8076ducc/robocup-2025/open/mechanical design/rpi & camera/lens aligner.3mf

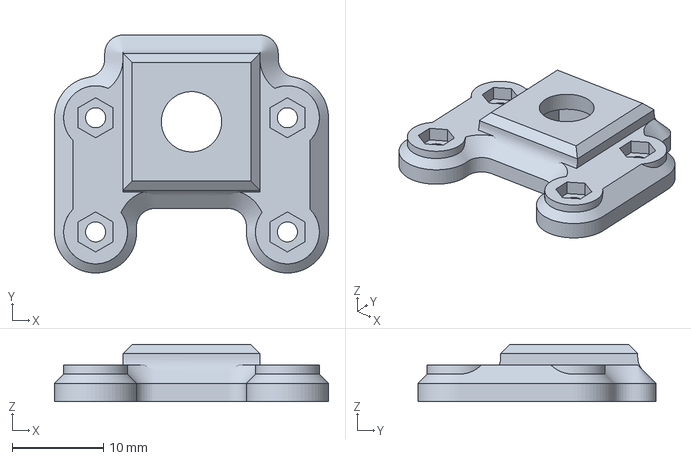
[picture p15: CAD file, 2025-03-22]
open/mechanical design/rpi & camera/lens aligner.3mf
30.0 x 26.1 x 6.25 mm
