8076ducc/robocup-2025/open/mechanical design/rpi & camera/nano b/rpi mount nano b.3mf

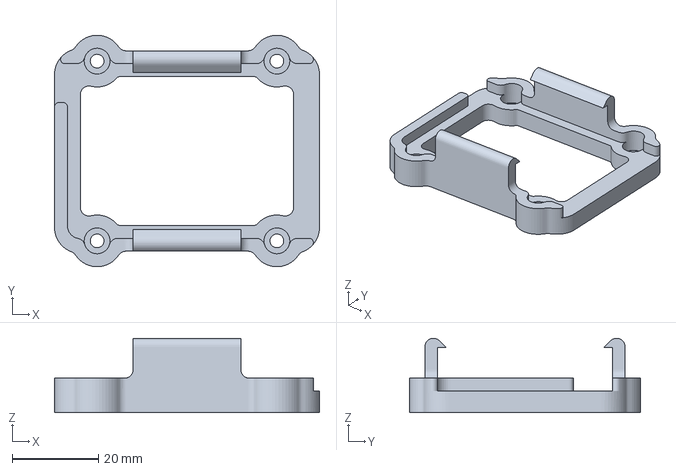
[picture p16: CAD file, 2025-02-21]
open/mechanical design/rpi & camera/nano b/rpi mount nano b.3mf
61.5 x 53.7 x 17.3 mm
