8076ducc/robocup-2025/open/mechanical design/spinning kicker/left plate.3mf

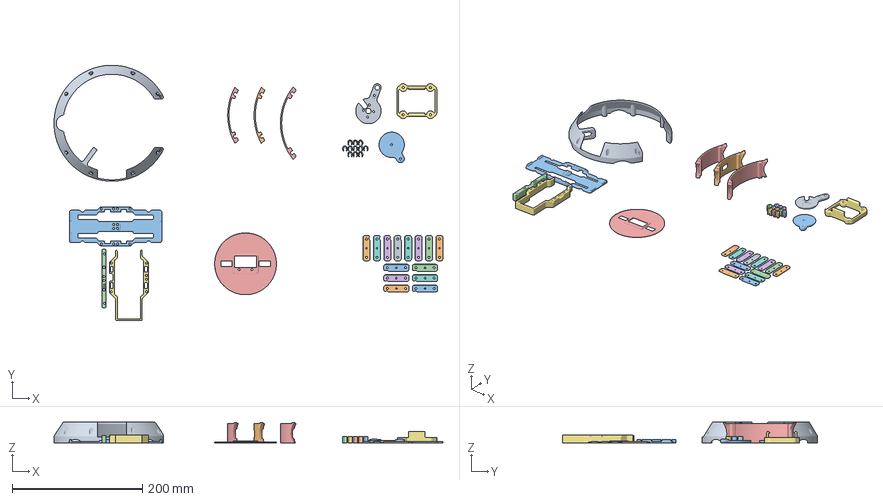
[picture p17: CAD file, 2025-02-01]
open/mechanical design/spinning kicker/left plate.3mf
597.6 x 392.4 x 32.0 mm
cover (layer 2)
motor spacer front x 4
driver cover (battery anti-short)
cover back (layer 1)
battery guide wall
motor spacer back left x 4
cover right (layer 1)
motor spacer back right x 6
layer 2 to 3 adapter
cover left (layer 1)
rpi mount
right plate
left plate
layer 1 short protection
wire clip x 11
