8076ducc/robocup-2025/open/mechanical design/wheel/4mm/wheel.3mf

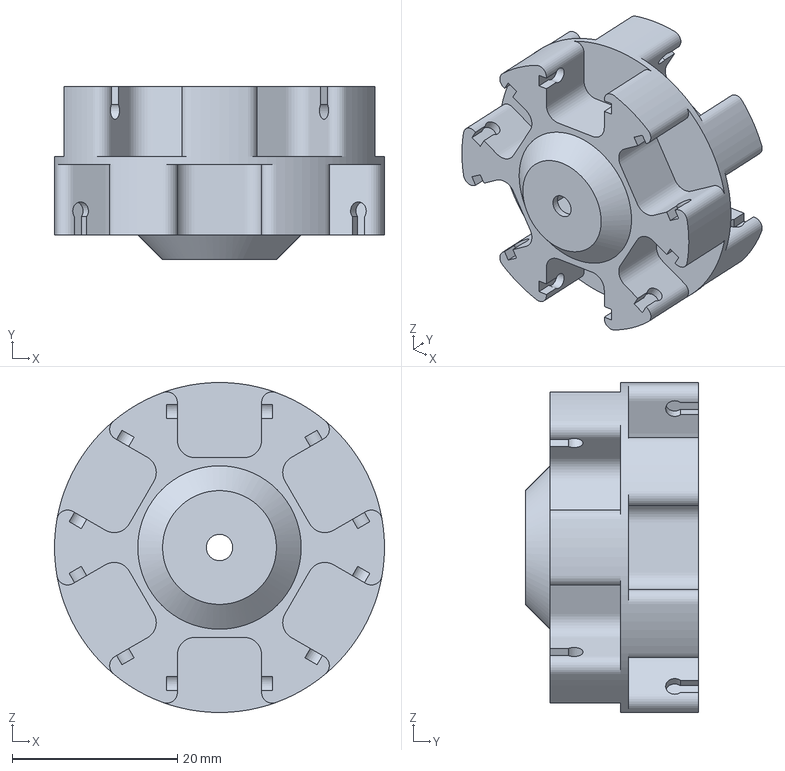
[picture p18: CAD file, 2025-06-07]
open/mechanical design/wheel/4mm/wheel.3mf
40.0 x 21.0 x 40.0 mm
