8076ducc/robocup-2025/open/mechanical design/wheel/5mm/wheel.3mf

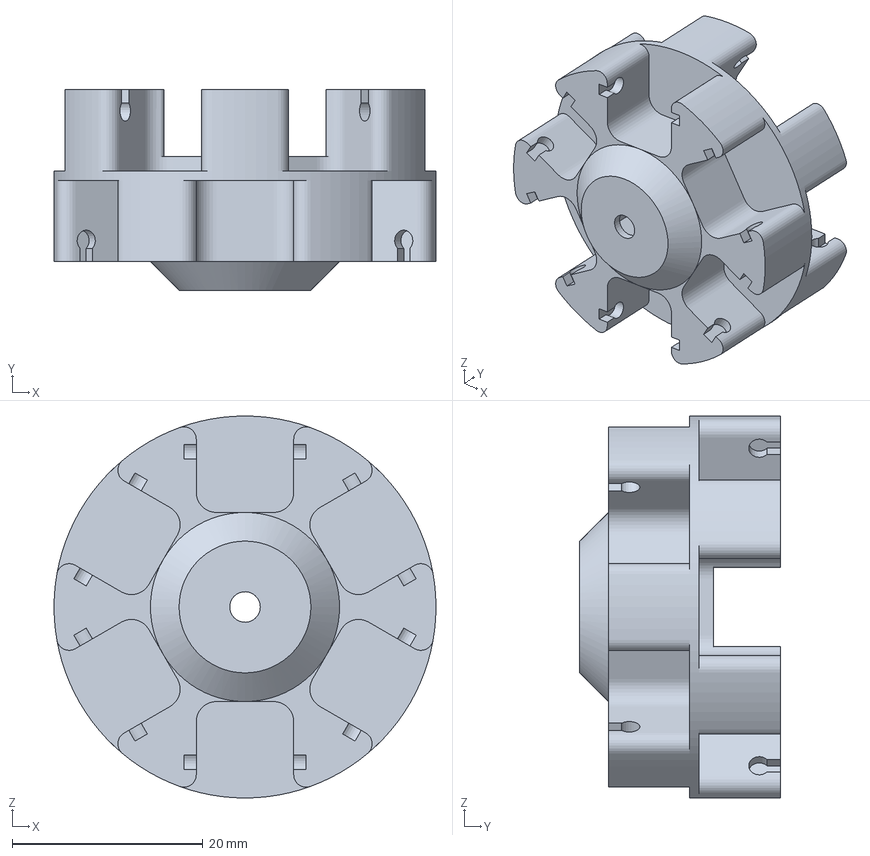
[picture p19: CAD file, 2025-02-01]
open/mechanical design/wheel/5mm/wheel.3mf
40.0 x 21.0 x 40.0 mm
