8076ducc/robocup-2025/open/mechanical design/wheel/motor spacer front.3mf

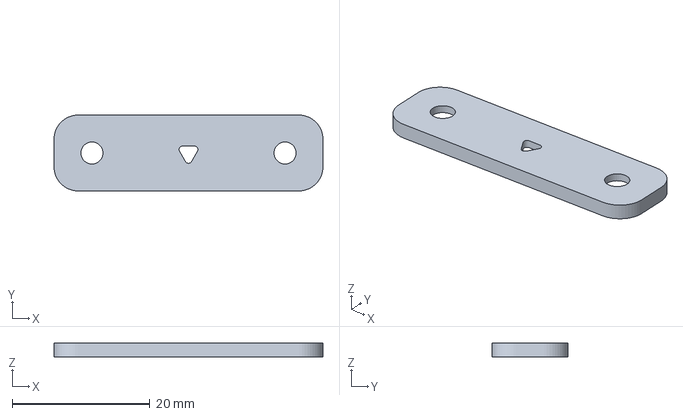
[picture p20: CAD file, 2025-02-01]
open/mechanical design/wheel/motor spacer front.3mf
39.0 x 11.0 x 2.00 mm
