8076ducc/robocup-2025/open/mechanical design/battery/battery guide wall.3mf

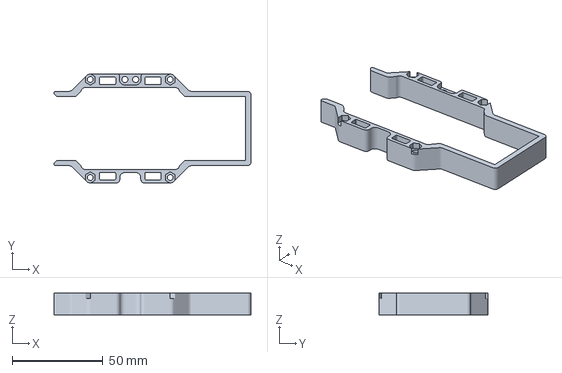
[picture p21: CAD file, 2025-01-22]
open/mechanical design/battery/battery guide wall.3mf
108.5 x 60.0 x 12.0 mm
