8076ducc/robocup-2025/open/mechanical design/cover/layer 1/servo mount.3mf

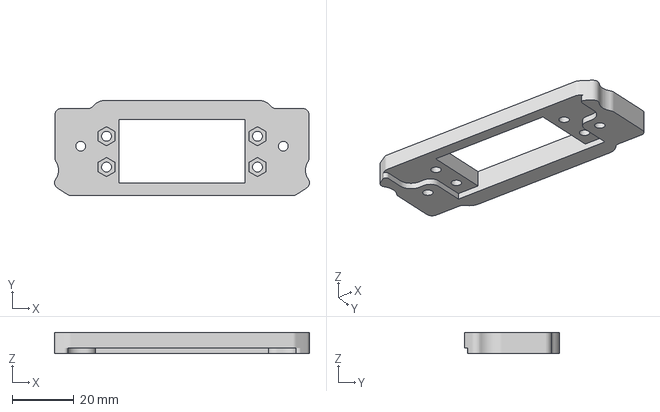
[picture p22: CAD file, 2025-03-22]
open/mechanical design/cover/layer 1/servo mount.3mf
82.8 x 30.9 x 6.90 mm
