8076ducc/robocup-2025/open/mechanical design/cover/layer 3/buck cover right.3mf

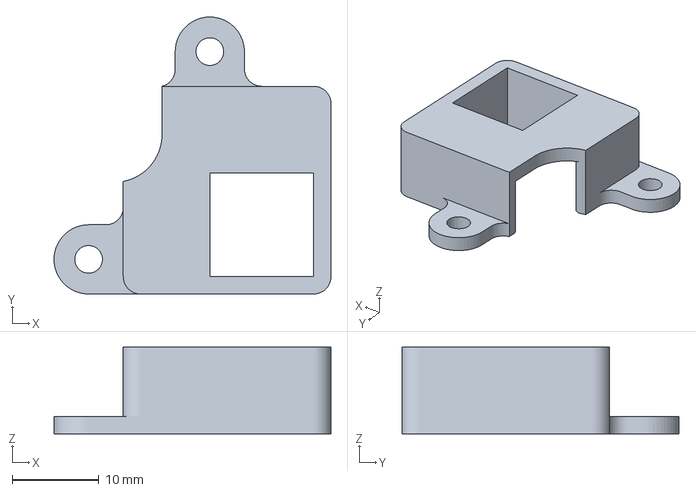
[picture p23: CAD file, 2025-06-07]
open/mechanical design/cover/layer 3/buck cover right.3mf
32.0 x 32.0 x 10.00 mm
