8076ducc/robocup-2025/open/mechanical design/kicker/ratchet.3mf

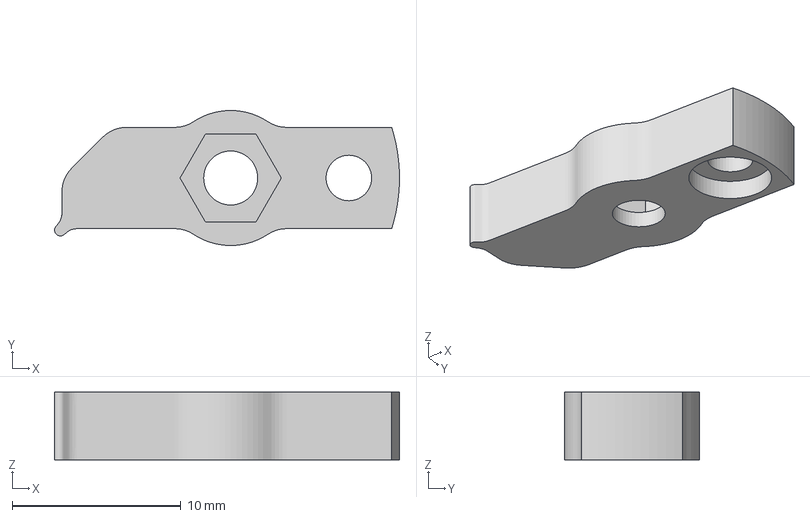
[picture p24: CAD file, 2025-06-07]
open/mechanical design/kicker/ratchet.3mf
20.4 x 8.00 x 4.00 mm
