8076ducc/robocup-2025/open/mechanical design/layer 4/layer 4.dxf

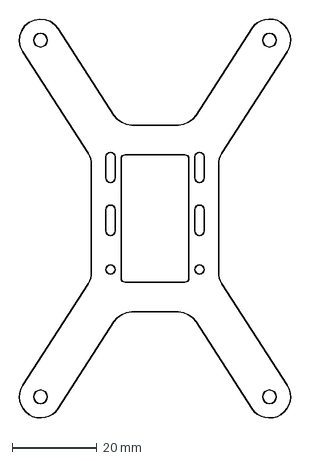
[picture p25: CAD file, 2025-03-12]
open/mechanical design/layer 4/layer 4.dxf
65.4 x 95.5 mm
