8076ducc/robocup-2025/open/mechanical design/layer 5/layer 5.1.dxf

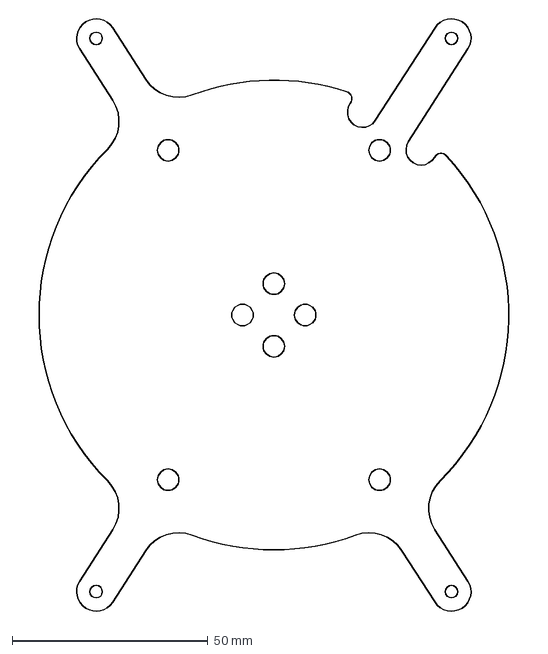
[picture p26: CAD file, 2025-03-12]
open/mechanical design/layer 5/layer 5.1.dxf
131.8 x 152.8 mm
