8076ducc/robocup-2025/open/mechanical design/rpi & camera/base a/rpi mount base a 7mm spacer.3mf

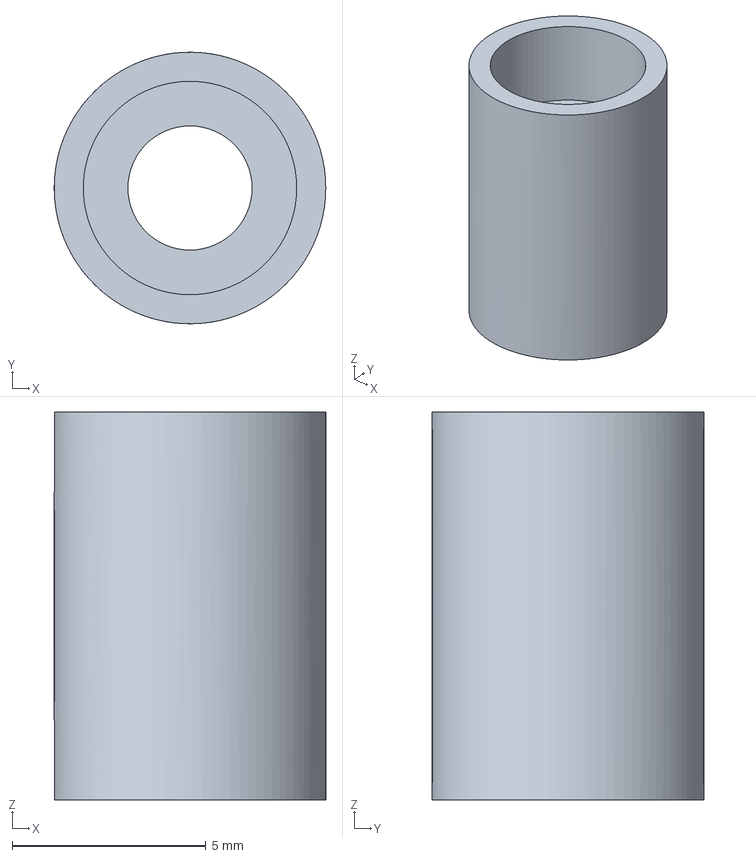
[picture p27: CAD file, 2025-03-03]
open/mechanical design/rpi & camera/base a/rpi mount base a 7mm spacer.3mf
7.00 x 7.00 x 10.0 mm
