8076ducc/robocup-2025/open/mechanical design/spinning kicker/right plate.3mf

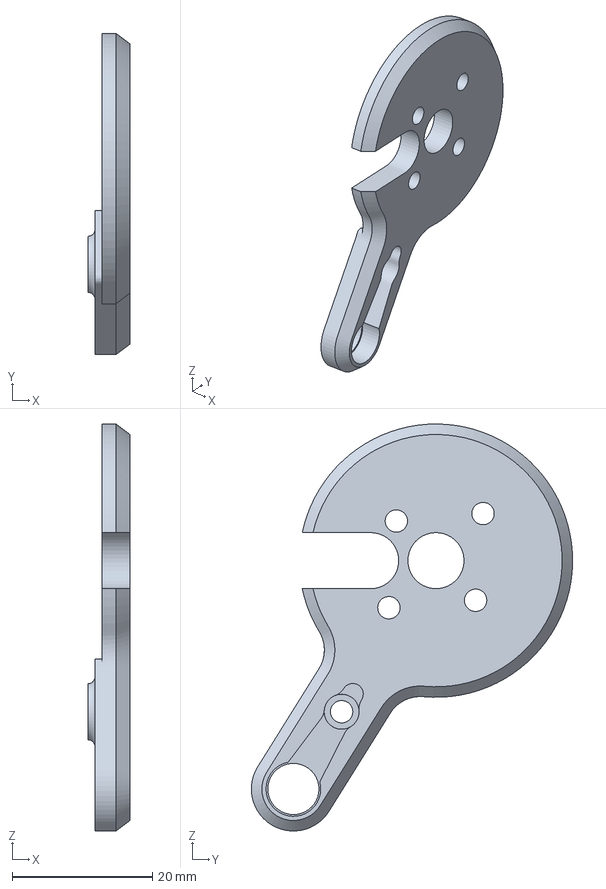
[picture p28: CAD file, 2025-02-01]
open/mechanical design/spinning kicker/right plate.3mf
6.00 x 45.8 x 58.1 mm
