8076ducc/robocup-2025/open/mechanical design/wheel/4mm/roller.3mf

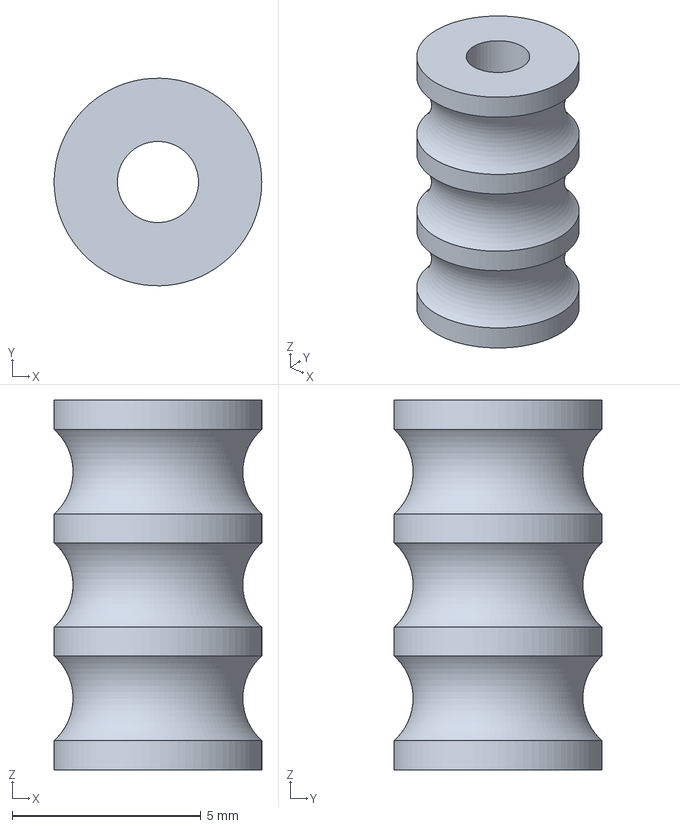
[picture p29: CAD file, 2025-03-03]
open/mechanical design/wheel/4mm/roller.3mf
5.50 x 5.50 x 9.80 mm
