8076ducc/robocup-2025/open/mechanical design/wheel/5mm/roller.3mf

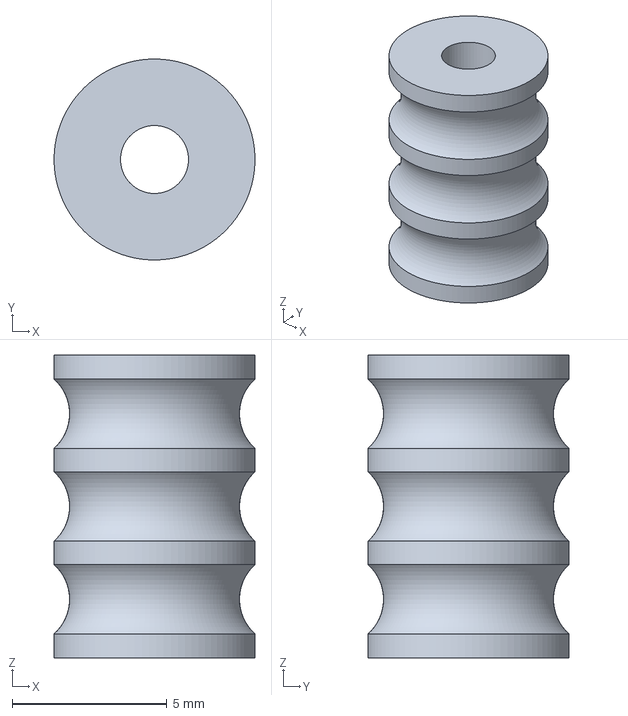
[picture p30: CAD file, 2025-01-22]
open/mechanical design/wheel/5mm/roller.3mf
6.50 x 6.50 x 9.80 mm
