8076ducc/robocup-2025/open/mechanical design/cover/layer 1/cover right (layer 1).3mf

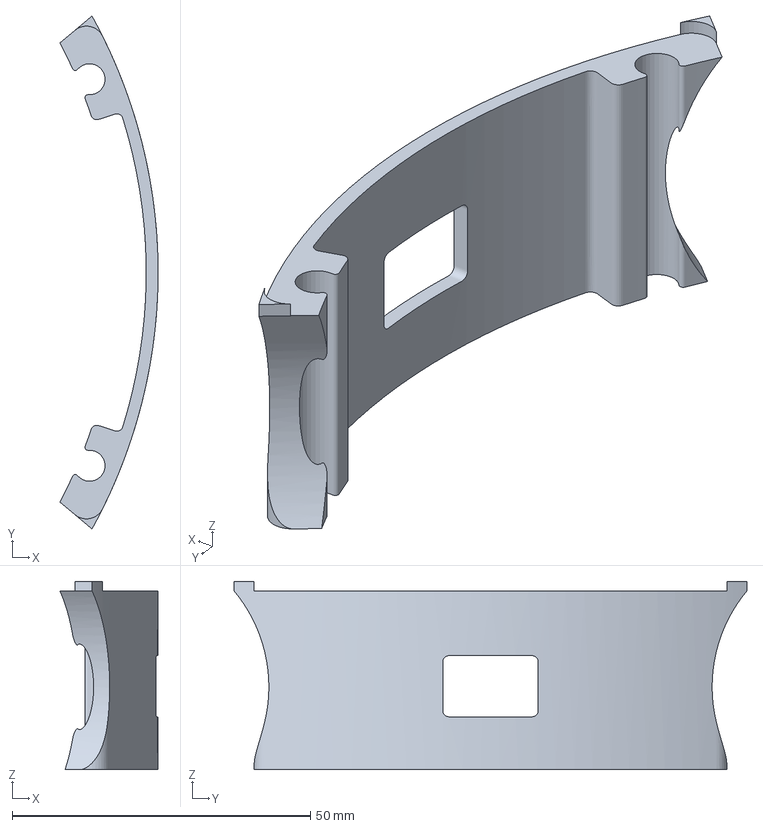
[picture p31: CAD file, 2025-02-01]
open/mechanical design/cover/layer 1/cover right (layer 1).3mf
16.5 x 86.1 x 31.6 mm
