8076ducc/robocup-2025/open/mechanical design/kicker/mirror sanding plate.3mf

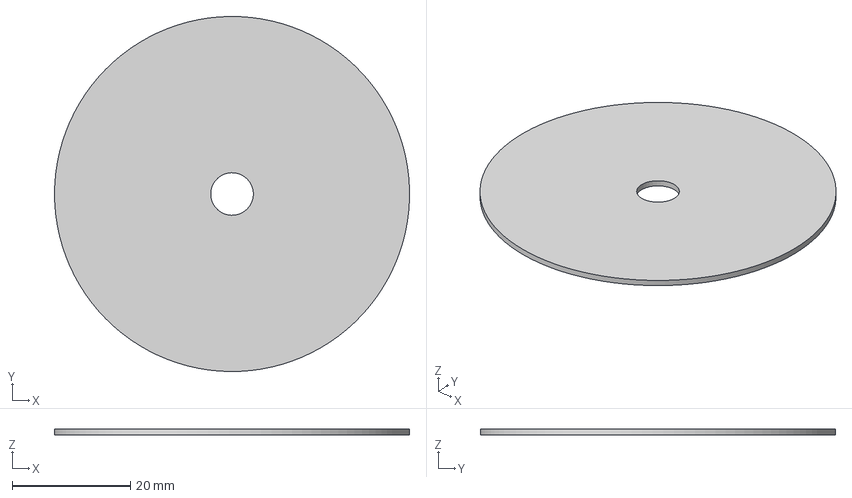
[picture p32: CAD file, 2025-06-07]
open/mechanical design/kicker/mirror sanding plate.3mf
60.0 x 60.0 x 1.00 mm
