8076ducc/robocup-2025/open/mechanical design/layer 5/layer 5.dxf

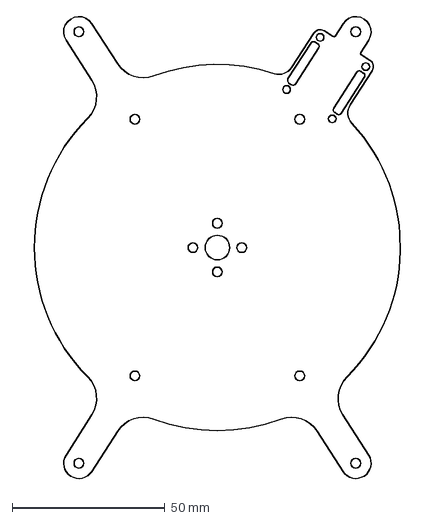
[picture p33: CAD file, 2025-03-12]
open/mechanical design/layer 5/layer 5.dxf
131.8 x 152.2 mm
