8076ducc/robocup-2025/open/mechanical design/misc/buck spacer.3mf

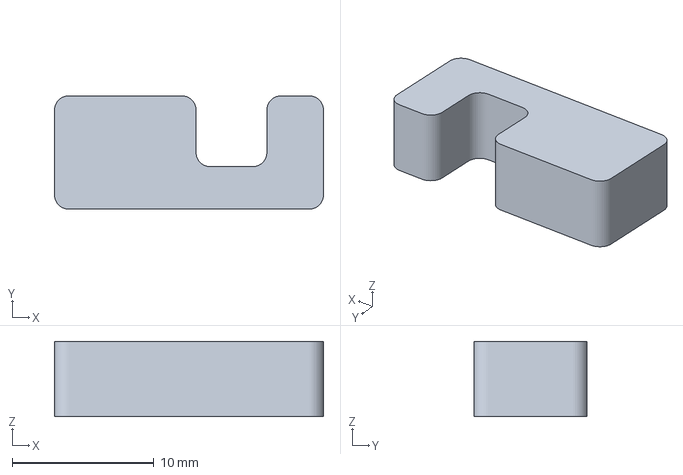
[picture p34: CAD file, 2025-06-07]
open/mechanical design/misc/buck spacer.3mf
19.0 x 8.00 x 5.30 mm
