8076ducc/robocup-2025/open/mechanical design/rpi & camera/base a/rpi mount base a lower.3mf

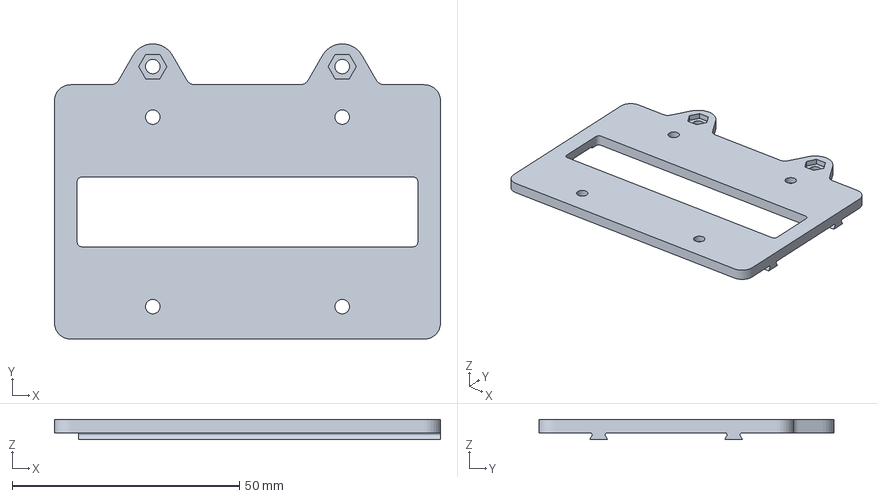
[picture p35: CAD file, 2025-02-28]
open/mechanical design/rpi & camera/base a/rpi mount base a lower.3mf
85.0 x 65.0 x 4.50 mm
