8076ducc/robocup-2025/open/mechanical design/spinning kicker/servo mount.3mf

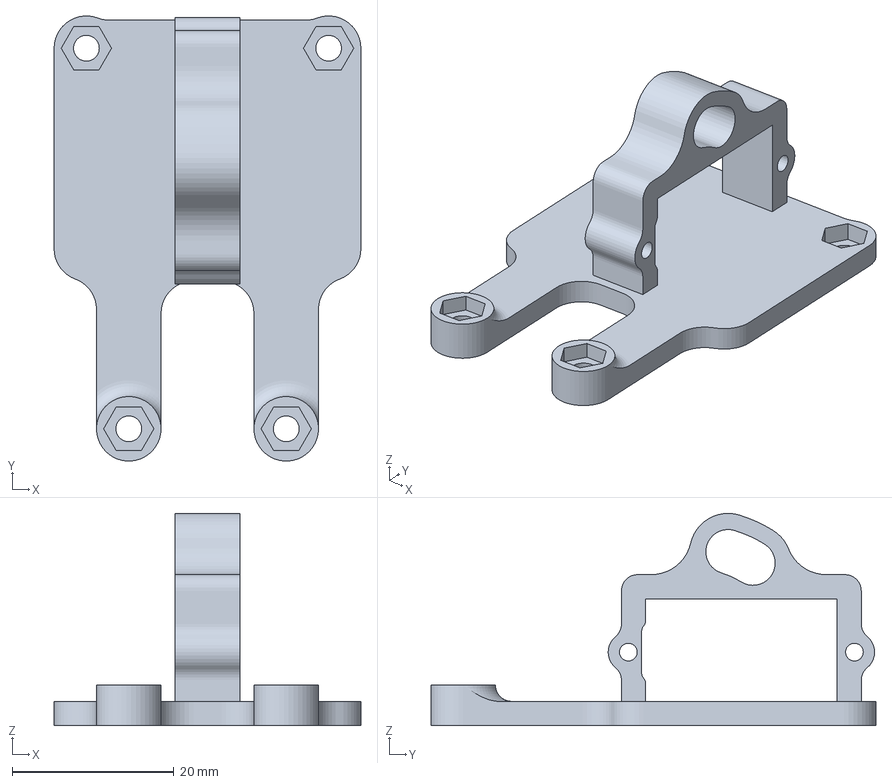
[picture p36: CAD file, 2025-02-01]
open/mechanical design/spinning kicker/servo mount.3mf
38.0 x 55.1 x 26.3 mm
