8076ducc/robocup-2025/open/mechanical design/cover/layer 1/cover left (layer 1).3mf

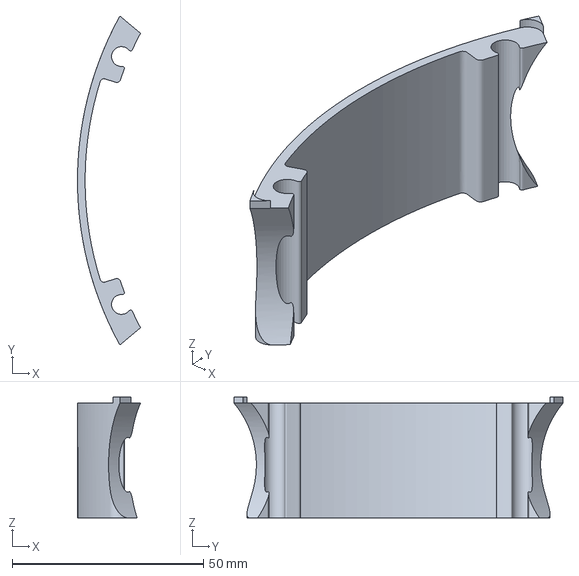
[picture p37: CAD file, 2025-01-11]
open/mechanical design/cover/layer 1/cover left (layer 1).3mf
16.5 x 86.1 x 31.6 mm
