8076ducc/robocup-2025/open/mechanical design/cover/layer 3/cover (layer 3).3mf

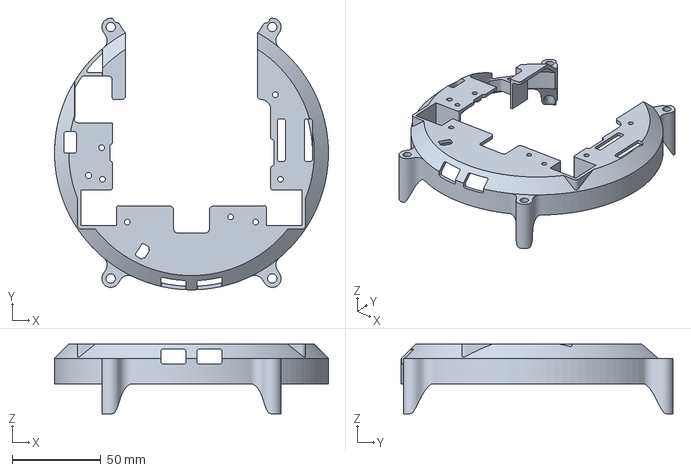
[picture p38: CAD file, 2025-06-07]
open/mechanical design/cover/layer 3/cover (layer 3).3mf
154.0 x 152.7 x 39.2 mm
