8076ducc/robocup-2025/open/mechanical design/kicker/gear rack.3mf

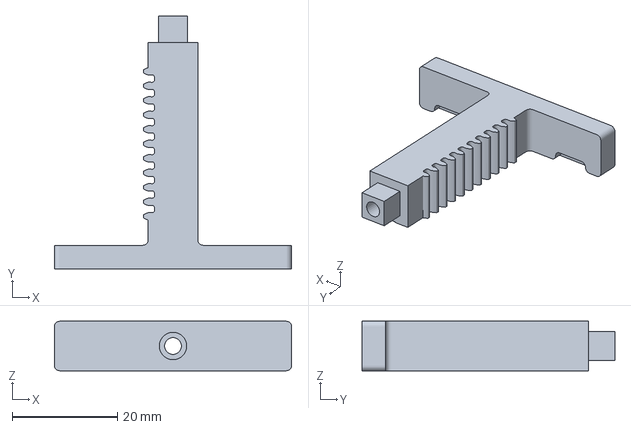
[picture p39: CAD file, 2025-06-07]
open/mechanical design/kicker/gear rack.3mf
45.0 x 48.0 x 9.40 mm
