8076ducc/robocup-2025/open/mechanical design/misc/mirror sawing plate.3mf

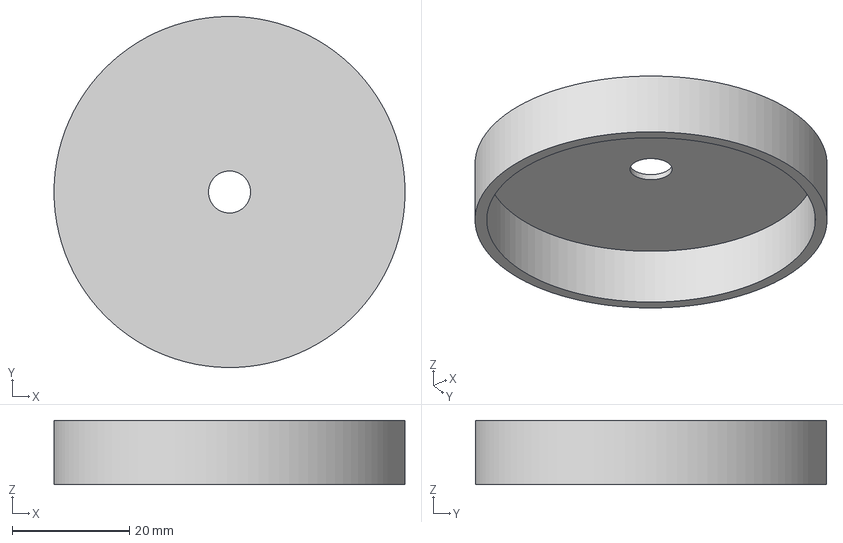
[picture p40: CAD file, 2025-06-07]
open/mechanical design/misc/mirror sawing plate.3mf
60.0 x 60.0 x 11.0 mm
