8076ducc/robocup-2025/open/mechanical design/rpi & camera/base a/ribbon cable clip.3mf

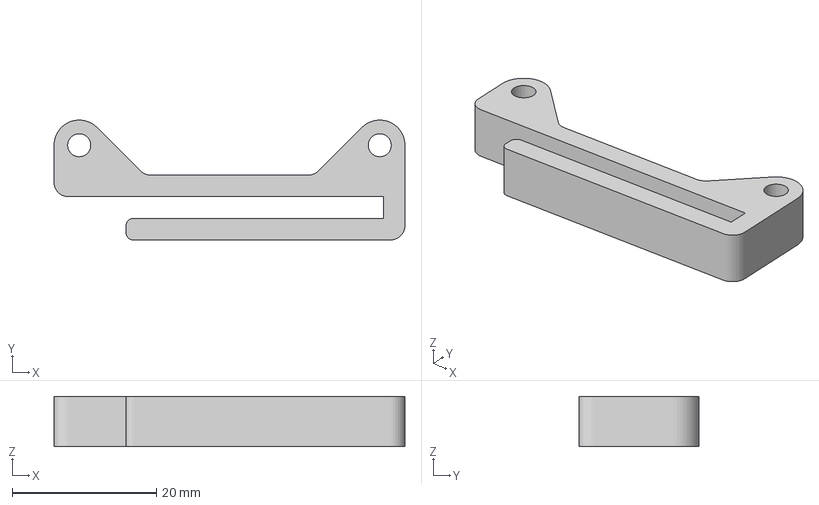
[picture p41: CAD file, 2025-02-21]
open/mechanical design/rpi & camera/base a/ribbon cable clip.3mf
48.7 x 16.6 x 7.00 mm
