8076ducc/robocup-2025/open/mechanical design/spinning kicker/mould lower.3mf

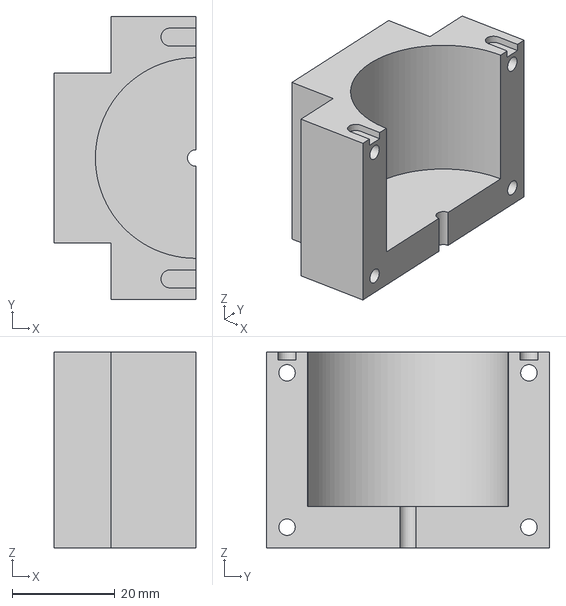
[picture p42: CAD file, 2025-01-22]
open/mechanical design/spinning kicker/mould lower.3mf
27.5 x 55.0 x 38.0 mm
