8076ducc/robocup-2025/open/mechanical design/cover/layer 1/cover back (layer 1).3mf

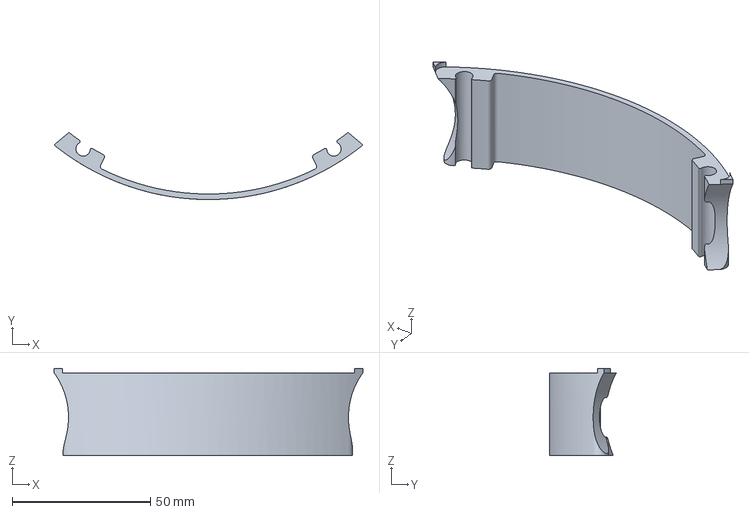
[picture p43: CAD file, 2025-01-11]
open/mechanical design/cover/layer 1/cover back (layer 1).3mf
111.8 x 24.3 x 31.6 mm
