8076ducc/robocup-2025/open/mechanical design/misc/layer 1 anti-short.3mf

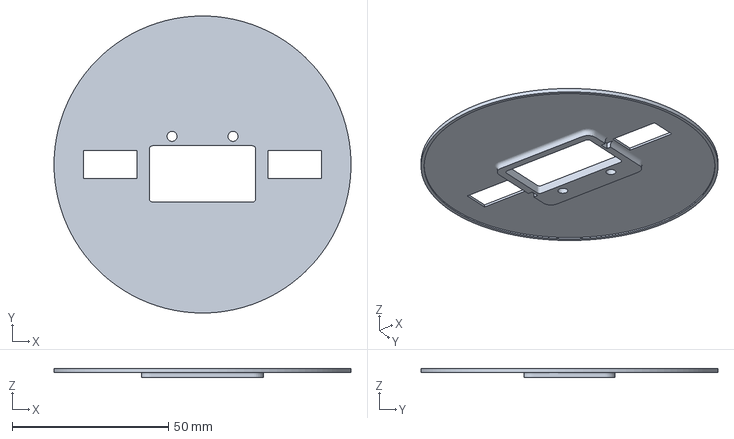
[picture p44: CAD file, 2025-02-21]
open/mechanical design/misc/layer 1 anti-short.3mf
95.0 x 95.0 x 2.80 mm
