8076ducc/robocup-2025/open/mechanical design/rpi & camera/base a/rpi mount base a 4mm spacer.3mf

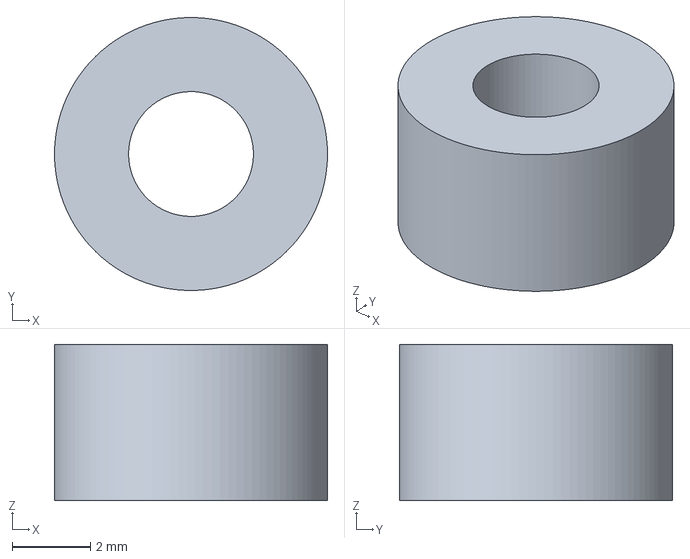
[picture p45: CAD file, 2025-02-21]
open/mechanical design/rpi & camera/base a/rpi mount base a 4mm spacer.3mf
7.00 x 7.00 x 4.00 mm
