8076ducc/robocup-2025/open/mechanical design/spinning kicker/mould cap.3mf

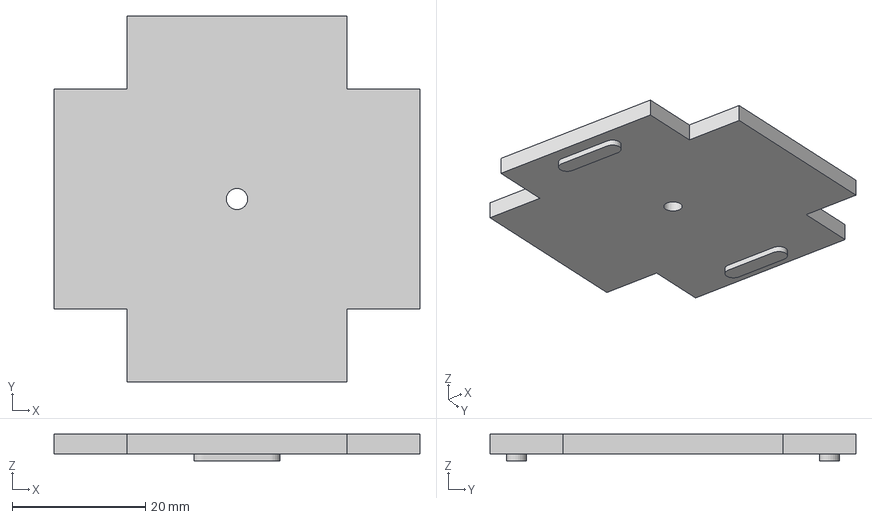
[picture p46: CAD file, 2025-01-22]
open/mechanical design/spinning kicker/mould cap.3mf
55.0 x 55.0 x 4.00 mm
