8076ducc/robocup-2025/open/mechanical design/kicker/bearing spacer.3mf

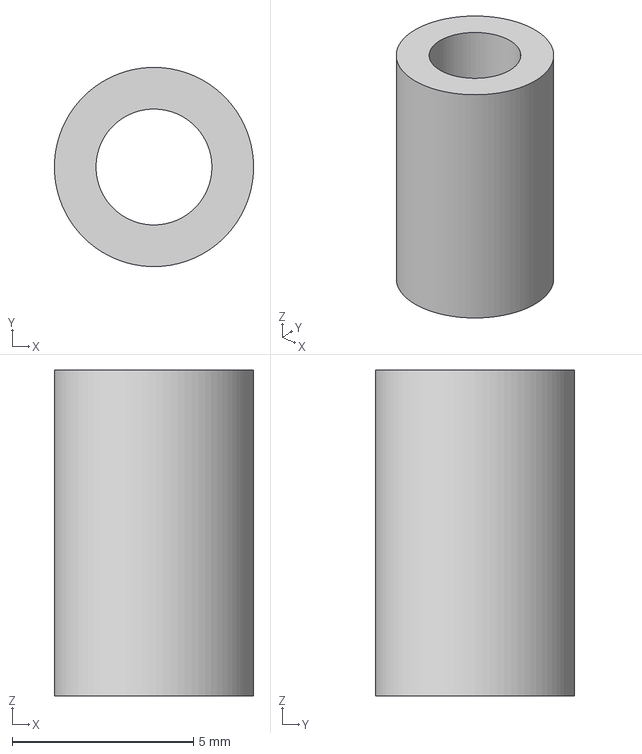
[picture p47: CAD file, 2025-06-07]
open/mechanical design/kicker/bearing spacer.3mf
5.50 x 5.50 x 9.00 mm
