8076ducc/robocup-2025/open/mechanical design/misc/buck support.3mf

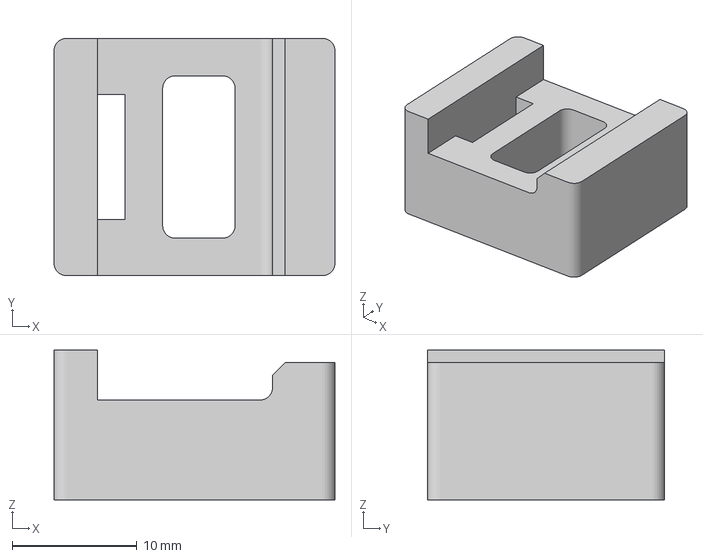
[picture p48: CAD file, 2025-02-21]
open/mechanical design/misc/buck support.3mf
22.5 x 19.0 x 12.0 mm
