8076ducc/robocup-2025/open/mechanical design/spinning kicker/roller.3mf

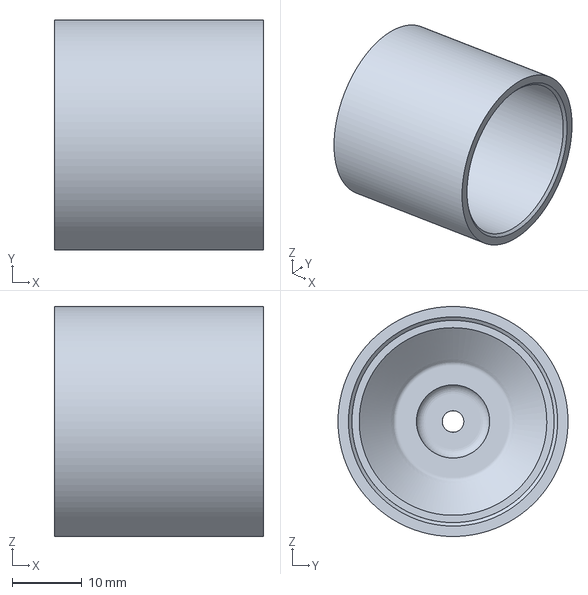
[picture p49: CAD file, 2025-01-22]
open/mechanical design/spinning kicker/roller.3mf
30.0 x 33.0 x 33.0 mm
