8076ducc/robocup-2025/open/mechanical design/kicker/ratchet (new).3mf

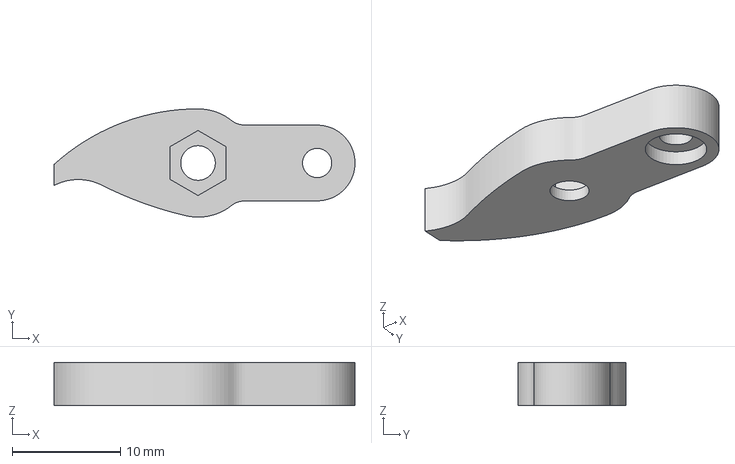
[picture p50: CAD file, 2025-06-07]
open/mechanical design/kicker/ratchet (new).3mf
27.8 x 10.00 x 4.00 mm
