8076ducc/robocup-2025/open/mechanical design/misc/layer 2 to 3 adapter.3mf

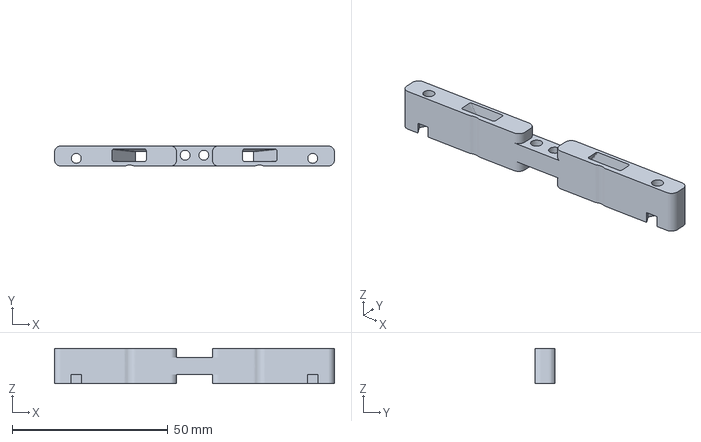
[picture p51: CAD file, 2025-02-01]
open/mechanical design/misc/layer 2 to 3 adapter.3mf
90.0 x 6.50 x 11.4 mm
