8076ducc/robocup-2025/open/mechanical design/kicker/slide case.3mf

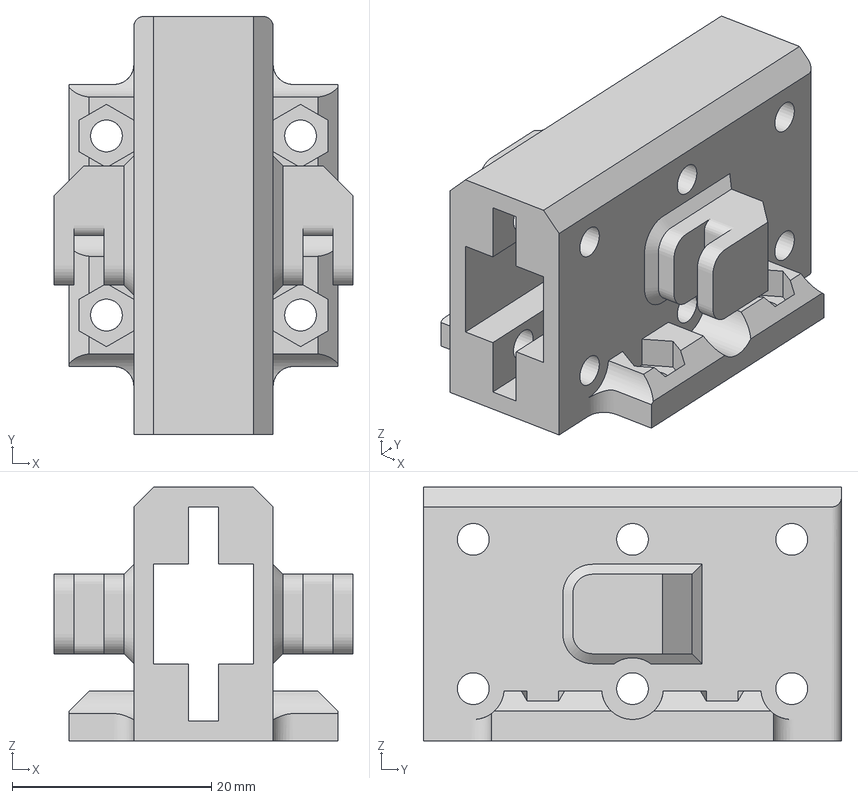
[picture p52: CAD file, 2025-06-07]
open/mechanical design/kicker/slide case.3mf
30.0 x 42.0 x 25.5 mm
