8076ducc/robocup-2025/open/mechanical design/misc/wire clip.3mf

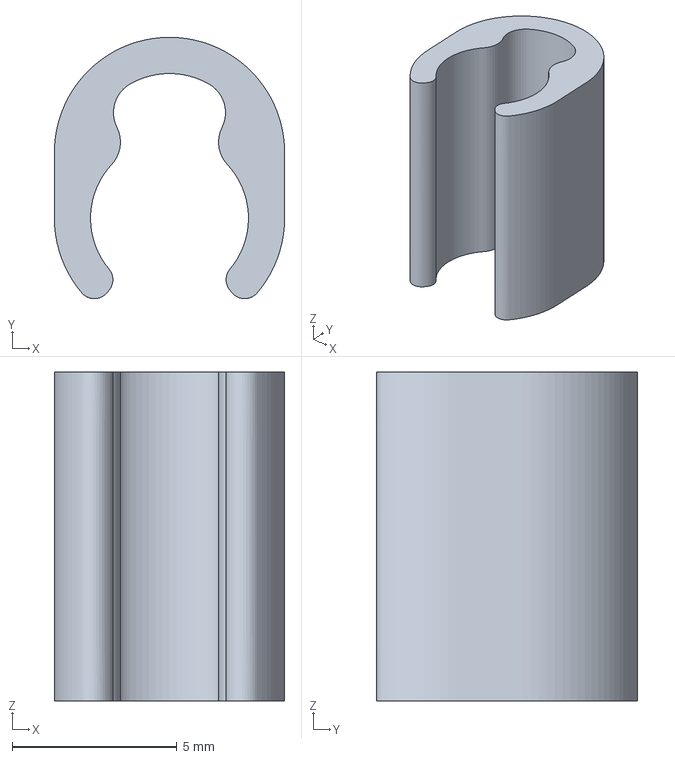
[picture p53: CAD file, 2025-01-22]
open/mechanical design/misc/wire clip.3mf
7.00 x 7.94 x 10.0 mm
