8076ducc/robocup-2025/open/mechanical design/kicker/slide.3mf

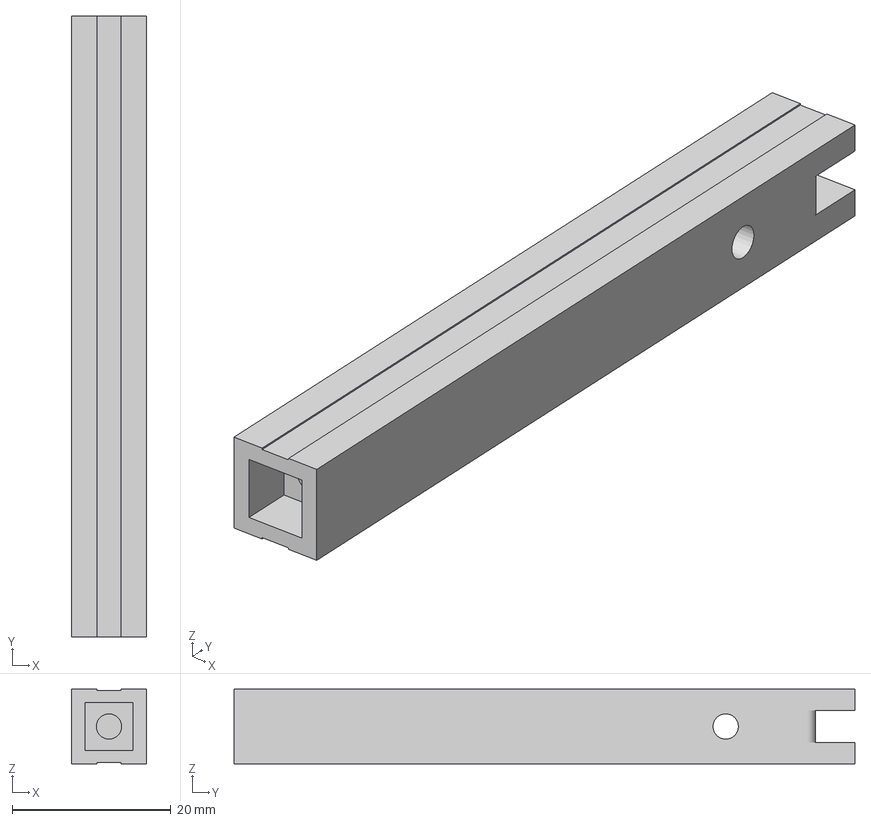
[picture p54: CAD file, 2025-06-07]
open/mechanical design/kicker/slide.3mf
9.40 x 78.3 x 9.40 mm
