8076ducc/robocup-2025/open/mechanical design/kicker/gear rack (extra teeth).3mf

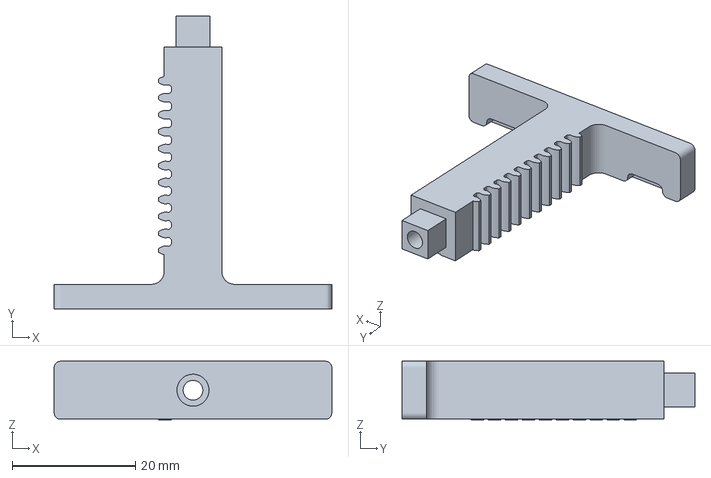
[picture p55: CAD file, 2025-06-07]
open/mechanical design/kicker/gear rack (extra teeth).3mf
45.0 x 47.5 x 9.50 mm
