8076ducc/robocup-2025/open/mechanical design/kicker/Spur Gear (12 teeth).3mf

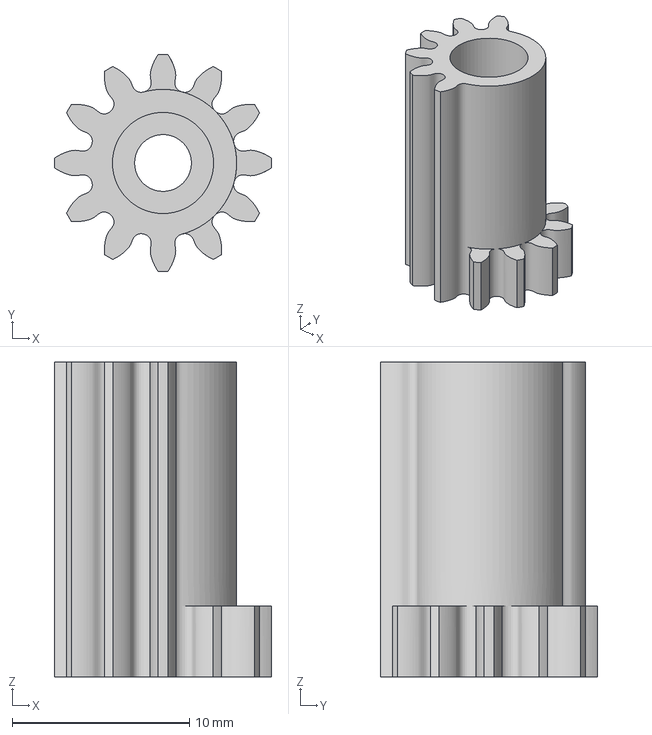
[picture p56: CAD file, 2025-06-07]
open/mechanical design/kicker/Spur Gear (12 teeth).3mf
12.2 x 12.2 x 17.8 mm
