8076ducc/robocup-2025/open/software design/microcontrollers/src/layer1/main.cpp

#include "main.h"
#include "light_ring.h"

PacketSerial TeensySerial;

Layer1TxDataUnion tx_data;
Layer1RxData rx_data;

LightRing light_ring;

void detectBall()
{
  Serial.println("Detect ball function running!");
  if (analogRead(LIGHTGATE) < ball_threshold)
  {
    tx_data.data.ball_in_catchment = true;
  }
  else
  {
    tx_data.data.ball_in_catchment = false;
  }
}

void onTeensyReceived(const byte *buf, size_t size)
{
  // Read the payload
  Layer1RxDataUnion data_received;
  // Don't continue if the payload is invalid
  if (size != sizeof(data_received))
  return;
  std::copy(buf, buf + size, std::begin(data_received.bytes));
  
  rx_data.line_track_ldr = data_received.data.line_track_ldr;
}

void setup()
{
  #ifdef SERIAL_DEBUG
  Serial.begin(serial_monitor_baud);
  while (!Serial)
  {
  }
  Serial.println("Debug serial connection established.");
  #endif
  
  light_ring.setup();
  pinMode(LIGHTGATE, INPUT);
  
  Serial0.begin(layer_1_serial_baud);
  // Serial0.setTxBufferSize(120);
  // Serial0.setRxBufferSize(120);
  while (!Serial0)
  {
  }
  TeensySerial.setStream(&Serial0);
  TeensySerial.setPacketHandler(&onTeensyReceived);
}

unsigned long last_time = 0;
int lowest = 3000;

void loop()
{
  #ifdef DEBUG
  //Serial.println("running Debug function::Calibrate");
  delay(150);
  // light_ring.calibrate();

  if (analogRead(LIGHTGATE) < lowest)
  {
    lowest = analogRead(LIGHTGATE);
  }
  Serial.println(analogRead(LIGHTGATE));
  Serial.print(lowest);
  Serial.print(" ");
  Serial.println(analogRead(LIGHTGATE));
  #else

  // Serial.println("im sending stuff to teensy1!");
  // TeensySerial.update();
  // Serial.println("attempting to run lightring_read");

  light_ring.read();
  detectBall();
  
  Serial.println("Sending data to Teensy1");
  TeensySerial.send(tx_data.bytes, sizeof(tx_data.bytes));
  #endif
}
