8076ducc/robocup-2025/open/software design/microcontrollers/src/layer1/main.h

#pragma once

#ifndef MAIN_H
#define MAIN_H

// #define DEBUG
// #define SERIAL_DEBUG
// #define BOT_A

#include <common.h>

#define S0 D2
#define S1 D3
#define S2 D4
#define S3 D5

#define MUX1 D0
#define MUX2 D1
#define LIGHTGATE D9

#define KICKER D10

// global variables

// TUNE THIS
const int ball_threshold = 1500;
// END TUNE

extern int line_track_ldr;
extern Layer1TxDataUnion tx_data;
extern Layer1RxData rx_data;

#endif
