8076ducc/robocup-2025/open/software design/microcontrollers/src/teensy1/camera.cpp

#include "main.h"

double field_width = 1580;
double field_height = 2190;

double regressGoal(double distance)
{
  return ((0 * pow(distance, 5)) + (0 * pow(distance, 4)) + (0.0017281976 * pow(distance, 3)) - (0.5748511944 * pow(distance, 2)) + (69.1097170904 * distance) - 2527.1180742143);
}

// store entire goal pose
void Robot::storeGoalPose(double yellow_goal_x, double yellow_goal_y, double blue_goal_x, double blue_goal_y)
{
  yellow_goal.current_pose.x = yellow_goal_x;
  yellow_goal.current_pose.y = yellow_goal_y;
  yellow_goal.current_pose.bearing = correctBearing(degrees(atan2(yellow_goal_x, yellow_goal_y)) + robot.current_pose.bearing);

  blue_goal.current_pose.x = blue_goal_x;
  blue_goal.current_pose.y = blue_goal_y;
  blue_goal.current_pose.bearing = correctBearing(degrees(atan2(blue_goal_x, blue_goal_y)) + robot.current_pose.bearing);
}

void Robot::storeYellowPose(double yellow_goal_x, double yellow_goal_y)
{
  yellow_goal.current_pose.x = yellow_goal_x;
  yellow_goal.current_pose.y = yellow_goal_y;
  yellow_goal.current_pose.bearing = correctBearing(degrees(atan2(yellow_goal_x, yellow_goal_y)) + robot.current_pose.bearing);
}

void Robot::storeBluePose(double blue_goal_x, double blue_goal_y)
{
  blue_goal.current_pose.x = blue_goal_x;
  blue_goal.current_pose.y = blue_goal_y;
  blue_goal.current_pose.bearing = correctBearing(degrees(atan2(blue_goal_x, blue_goal_y)) + robot.current_pose.bearing);
}

// store open goal pose
void Robot::storeGoalOpenPose(double yellow_open_x, double yellow_open_y, double blue_open_x, double blue_open_y)
{
  yellow_open.current_pose.x = yellow_open_x;
  yellow_open.current_pose.y = yellow_open_y;
  yellow_open.current_pose.bearing = correctBearing(degrees(atan2(yellow_open_x, yellow_open_y)) + robot.current_pose.bearing);

  blue_open.current_pose.x = blue_open_x;
  blue_open.current_pose.y = blue_open_y;
  blue_open.current_pose.bearing = correctBearing(degrees(atan2(blue_open_x, blue_open_y)) + robot.current_pose.bearing);
}

void Robot::storeYellowOpenPose(double yellow_open_x, double yellow_open_y)
{
  yellow_open.current_pose.x = yellow_open_x;
  yellow_open.current_pose.y = yellow_open_y;
  yellow_open.current_pose.bearing = correctBearing(degrees(atan2(yellow_open_x, yellow_open_y)) + robot.current_pose.bearing);
}

void Robot::storeBlueOpenPose(double blue_open_x, double blue_open_y)
{
  blue_open.current_pose.x = blue_open_x;
  blue_open.current_pose.y = blue_open_y;
  blue_open.current_pose.bearing = correctBearing(degrees(atan2(blue_open_x, blue_open_y)) + robot.current_pose.bearing);
}

void Robot::storeRobotPose()
{
  double ema_const = 0.2;

  double yellow_goal_real_dist = regressGoal(sqrt(pow(yellow_goal.current_pose.x, 2) + pow(yellow_goal.current_pose.y, 2)));
  double yellow_goal_real_x = yellow_goal_real_dist * sin(radians(yellow_goal.current_pose.bearing));
  double yellow_goal_real_y = yellow_goal_real_dist * cos(radians(yellow_goal.current_pose.bearing));

  double blue_goal_real_dist = regressGoal(sqrt(pow(blue_goal.current_pose.x, 2) + pow(blue_goal.current_pose.y, 2)));
  double blue_goal_real_x = blue_goal_real_dist * sin(radians(blue_goal.current_pose.bearing));
  double blue_goal_real_y = blue_goal_real_dist * cos(radians(blue_goal.current_pose.bearing));

  if (yellow_goal.detected && blue_goal.detected)
  {
    robot.current_pose.x = -(yellow_goal_real_x + blue_goal_real_x) / 2;
    robot.current_pose.y = -(yellow_goal_real_y + blue_goal_real_y) / 2;
  }
  else if (yellow_goal.detected)
  {
    robot.current_pose.x = -yellow_goal_real_x;

    robot.current_pose.y = (yellow_goal.current_pose.y >= 0) ? (field_height / 2) - yellow_goal_real_y : -(field_height / 2) - yellow_goal_real_y;
  }
  else if (blue_goal.detected)
  {
    robot.current_pose.x = -blue_goal_real_x;

    robot.current_pose.y = (blue_goal_real_y >= 0) ? (field_height / 2) - blue_goal_real_y : -(field_height / 2) - blue_goal_real_y;
  }

  robot.current_pose.x = (robot.current_pose.x * ema_const) + (previous_pose.x * (1 - ema_const));
  robot.current_pose.y = (robot.current_pose.y * ema_const) + (previous_pose.y * (1 - ema_const));

  previous_pose.x = robot.current_pose.x;
  previous_pose.y = robot.current_pose.y;
}
