8076ducc/robocup-2025/open/software design/microcontrollers/include/serial.h

#pragma once

#ifndef SHARED_H
#define SHARED_H

#include "utils.h"

const int serial_baud = 512000;
const int bt_serial_baud = 115200;
const int cam_serial_baud = 500000; // 2000000 originally
const int imu_serial_baud = 512000;
const int layer_1_serial_baud = 256000; // 512000 originally
const int teensy1_serial_baud = 2000000;
const int serial_monitor_baud = 512000;

struct BtTxData
{
    bool ball_detected;
    Pose ball_pose;
    bool robot_detected;
    Pose robot_pose;
};

struct BtRxData
{
    bool ball_detected;
    Pose ball_pose;
    Pose robot_pose;
};

struct CamTxData
{
    bool ball_detected;
    int ball_x;
    int ball_y;
    bool yellow_goal_detected;
    int yellow_goal_x;
    int yellow_goal_y;
    int yellow_open_x;
    int yellow_open_y;
    bool blue_goal_detected;
    int blue_goal_x;
    int blue_goal_y;
    int blue_open_x;
    int blue_open_y;
    double fps;
};

struct CamRxData
{
    bool track_orange;
    bool track_yellow;
    bool track_blue;
};

struct ImuTxData
{
    double bearing;
};

struct ImuRxData
{
};

struct Layer1TxData
{
    bool on_line;
    double line_angle;
    double chord_length;
    double line_centre;
    int line_track_error;
    bool ball_in_catchment;
    bool kicker_out;
    int line_start_ldr;
    int line_end_ldr;
};

struct Layer1RxData
{
    bool kick;
    int line_track_ldr;
};

struct Teensy1TxData
{
    double bearing;
};

struct Teensy1RxData
{
    bool robot_detected;

    Pose current_pose;
    Pose target_pose;

    Goal yellow_goal;
    Goal blue_goal;

    bool ball_detected;

    bool dip_1_on;
    bool dip_2_on;
    bool dip_3_on;
    bool dip_4_on;
};

union BtTxDataUnion
{
    BtTxData data;
    byte bytes[sizeof(BtTxData)];

    BtTxDataUnion() : data() {}
};

union BtRxDataUnion
{
    BtRxData data;
    byte bytes[sizeof(BtRxData)];

    BtRxDataUnion() : data() {}
};

union CamTxDataUnion
{
    CamTxData data;
    byte bytes[sizeof(CamTxData)];

    CamTxDataUnion() : data() {}
};

union CamRxDataUnion
{
    CamRxData data;
    byte bytes[sizeof(CamRxData)];

    CamRxDataUnion() : data() {}
};

union ImuTxDataUnion
{
    ImuTxData data;
    byte bytes[sizeof(ImuTxData)];

    ImuTxDataUnion() : data() {}
};

union ImuRxDataUnion
{
    ImuRxData data;
    byte bytes[sizeof(ImuRxData)];

    ImuRxDataUnion() : data() {}
};

union Layer1TxDataUnion
{
    Layer1TxData data;
    byte bytes[sizeof(Layer1TxData)];

    Layer1TxDataUnion() : data() {}
};

union Layer1RxDataUnion
{
    Layer1RxData data;
    byte bytes[sizeof(Layer1RxData)];

    Layer1RxDataUnion() : data() {}
};

union Teensy1TxDataUnion
{
    Teensy1TxData data;
    byte bytes[sizeof(Teensy1TxData)];

    Teensy1TxDataUnion() : data() {}
};

union Teensy1RxDataUnion
{
    Teensy1RxData data;
    byte bytes[sizeof(Teensy1RxData)];

    Teensy1RxDataUnion() : data() {}
};

#endif
